dvellon/cueloop/submissions/autodesk_application/APPLICATION_CHECKLIST.md

# Autodesk application submission checklist

Deadline: **September 7, 2026 at 11:59 PM PDT**. Target an internal submission no later than September 6.

## Digital package gate

- [x] Recheck official overview, rules, and organizer guide; record any change.
- [x] Replace only truthful personal facts in application response 5.
- [x] Create the public Hackster opening and paste its URL into response 3.
- [x] Add name, elevator pitch, concept render, BOM, and complete opening story.
- [x] Add Arduino UNO Q, Autodesk Fusion, and PCBWay 3D Printing to Things.
- [x] Complete `HARDWARE_TESTS.md` C-100 through C-109 using `cad/FUSION_WINDOWS_RUNBOOK.md`; attach the genuine native-history `.f3d` only after component/timeline/parameter/geometry/reopen checks and retain the hashed return bundle.
- [x] Attach or embed the system diagram and concept-render disclosure.
- [x] Ensure every “built/measured/tested” claim has evidence; keep future work in future tense.
- [x] Confirm the project is handheld/carryable, carry-on-safe in concept, useful beyond AU, and relevant to Autodesk customers.
- [x] Explain why UNO Q, Fusion, and PCBWay each materially matter.
- [x] Confirm V2 differentiation from CueLoop V1 is explicit.
- [x] Check licenses/provenance for every image, model, code link, and attachment.

## Account-controlled final action

- [ ] Preview the application and project while logged out or in a private browser window.
- [ ] Save a local PDF/screenshot of the live rules if template placeholders remain.
- [ ] Save a copy of each final pasted answer.
- [ ] Submit before the deadline and capture the confirmation page/time.
- [ ] Record the submitted URL and confirmation in `STATUS.md` without personal data.
