dvellon/cueloop/submissions/autodesk_application/APPLICATION_RESPONSES.md

# CueLoop Bridge — Autodesk hardware application responses

**Recommended product name:** CueLoop Bridge  
**One-sentence pitch:** A private, pocketable acoustic awareness bridge that lets creators notice the door, a timer, a collaborator, or a machine finishing in another space—without cloud microphones or stored audio.  
**Short elevator pitch:** Clip on the CueLoop Bridge receiver and leave its detachable CuePod beside what matters. Arduino UNO Q classifies acoustic events locally, checks uncertain evidence over time, and turns confirmed events into a calm visual and haptic cue, while raw audio disappears after inference.

The answers below map to the five prompts in Hackster's organizer-authored application guide. Recheck the live form before pasting.

## 1. What are you going to build?

I am going to build **CueLoop Bridge**, a compact smart accessory that helps people remain aware of important acoustic events occurring somewhere else. The system has two physically related pieces: a small detachable wireless CuePod placed near a door, timer, printer, CNC machine, test rig, or collaborator, and a portable receiver built around Arduino UNO Q. The receiver clips to a belt or bag, hangs from a lanyard, or rests on its integrated desk stand. When the pod hears a selected event, the UNO Q processes it locally and presents a discreet, understandable visual and haptic cue.

The core interaction is deliberately simple: place the pod, choose what matters, and carry the receiver. A wide diffused light communicates urgency and event family, a haptic pattern works while the receiver is clipped or a user is wearing hearing protection, and tactile controls acknowledge, mute, or change priority without opening an app. The CuePod docks mechanically into the receiver for transport; charging contacts and the final power-path design remain measured hardware-development gates. The enclosure is designed as a serviceable Autodesk Fusion assembly with a protected microphone path, USB access, battery restraint, internal board supports, and a clip that doubles as a stand.

CueLoop Bridge is carry-on-safe and useful well beyond Autodesk University. It is intended for designers, makers, technicians, caregivers, people who are deaf or hard of hearing, headphone users, and anyone who moves between acoustically separated spaces.

## 2. What problem will it solve? How is it different, and why is it useful?

Many useful sounds demand attention without requiring anyone to listen continuously: a printer finishes, a timer beeps, someone knocks, water keeps running, or a collaborator calls from another room. Today the person often has to remain nearby, repeatedly check, turn up a loud alert, or place an internet-connected smart speaker or camera in the space. Those compromises are especially costly for people who are deaf or hard of hearing, workers wearing hearing protection, and creators who need to focus deeply.

CueLoop Bridge moves awareness instead of recording a room. Its microphone pod is designed to send short-lived acoustic evidence over the local network to Arduino UNO Q. Edge AI maps the sound into a small user-selected vocabulary, and an uncertainty-aware event engine combines several windows before deciding. A borderline result enters a visible confirmation period rather than creating an instant false alarm. Only a confirmed event, time, confidence, pod location, and user feedback are kept; raw audio is discarded after inference by default.

That combination is the differentiation: detached placement, portable output, local processing, no default recording archive, and deliberate treatment of uncertainty. Smart speakers emphasize general voice services and the cloud. Baby monitors and cameras expose more private context than this task needs. Simple sound classifiers often flash a label for every model spike. CueLoop Bridge is a focused awareness tool that asks, “Is this important enough and certain enough to interrupt this person?”

The product is not a certified alarm, security system, or medical device and will not be marketed as a replacement for required safety equipment. It is useful because it gives users calmer control over ordinary awareness while protecting concentration and privacy.

## 3. Link to the project you have started

https://www.hackster.io/danvellon/cueloop-bridge-69f47f

## 4. How does your solution work? What are the main features? How will UNO Q, Fusion, and PCBWay be used?

The detachable CuePod firmware is designed to use the digital microphone on a Seeed Studio XIAO ESP32S3 Sense to capture 16 kHz mono audio and send sequence-numbered, timestamped frames over a trusted local Wi-Fi network. The Arduino UNO Q Linux side receives those frames into a bounded jitter buffer, normalizes model windows, and runs a lightweight audio-event model locally. A second decision layer then applies per-event confidence thresholds, user priority, temporal confirmation, hysteresis, and cooldown. This prevents a single uncertain window from becoming an immediate interruption.

When the event engine confirms something important, the Linux application creates a structured event record and updates a local, high-contrast dashboard. Through Arduino Bridge RPC it also sends a compact command to the UNO Q's STM32U585 microcontroller. The MCU owns deterministic LED, haptic, and optional buzzer timing and reads the acknowledgement control even if the higher-level UI is busy. This is a genuine use of the UNO Q's dual-processor architecture: the Qualcomm Linux side handles Wi-Fi, AI, policy, history, and the local interface, while the STM32 handles immediate physical interaction and health indication.

The product's main features are a dockable room-to-room microphone pod; local-first AI; confidence-aware confirmation; user-selected event priority; nonverbal visual and haptic cues; local feedback for later threshold personalization; health/loss/latency diagnostics; and no raw-audio retention by default. A simulator and replay harness make the complete pipeline testable even before hardware is available.

Autodesk Fusion is not an afterthought. It is the source of truth for the mechanical system: named dimensional parameters; CuePod base and lid; protected microphone labyrinth; USB opening; battery cavity and strain relief; XIAO supports; receiver base and lid; UNO Q mounting and connector clearance; diffused alert window; tactile controls; clip/stand hinge; pod dock; fasteners; and assembly clearances. The reviewed generator has produced a genuine native-history preliminary `.f3d`. I inspected its Browser hierarchy, timeline, parameters, sections, clearances, and interference results; verified that one parameter updates all seven microphone ports; and then closed and reopened it cleanly. Physical measurements and fit tests will drive named parameters rather than manual remodels. The final design will add Fusion Electronics for an interconnect/carrier, an assembly and drawing package, and DFM variants.

PCBWay will be used to manufacture the evolved enclosure and, if the carrier proves justified, its PCB/assembly. The first enclosure is designed for a serviceable printed prototype with realistic walls, clearances, M2 fasteners, accessible USB ports, and separate lids. DFM work will compare SLS/MJF-style printing with a future injection-molded split, reduce support and fastener count, add draft and consistent wall sections, define material/finish, and create a repeatable end-of-line fit and function test appropriate to a product that could be built in approximately 750 units.

## 5. Tell us about yourself and why you can complete it

I am an investment banker who spends most of my time on professional work and technology research. My work requires disciplined systems thinking, careful review, and the ability to execute complex projects against deadlines. Outside my professional role, I am a hobbyist hardware and software developer with experience in system design and a willingness to learn across electronics, software, and mechanical design.

CueLoop grew from a recurring personal frustration. When work calls me into another room, I can miss the toaster, microwave, or washing machine finishing and leave something waiting or unattended. A similar problem occurs professionally when a long print job runs out of paper unnoticed: work that appeared to be progressing has actually stopped, creating an avoidable delay. These experiences give me a direct understanding of the problem CueLoop Bridge addresses and a practical focus on making its alerts calm, useful, and reliable.

I have already ordered the core Arduino UNO Q and XIAO Sense hardware, created a simulator-first architecture so shipping cannot stop software work, built a safety and privacy plan, and generated and digitally validated a native parametric Fusion design. My development approach is evidence-driven: simulated, development-computer, UNO Q, and physical-CuePod results are labeled separately, and features that do not meet their evaluation targets will be revised or removed rather than overclaimed. I will use the development period for physical integration, Fusion Electronics, PCBWay enclosure iterations, portable-interaction testing, and a complete reproducible build story.
