dvellon/cueloop/submissions/autodesk_application/PACKAGE_README.md

# CueLoop Bridge preliminary Autodesk application kit

This directory is the source for the September 7, 2026 Autodesk hardware
application. The generated archive records its exact Git commit and per-file
SHA-256 hashes.

## Recommended public project uploads

1. Use `media/20-hero-pod-detached.png` as the cover.
2. Paste `01-HACKSTER_PROJECT_OPENING.md` into the project story and adapt only
   formatting required by Hackster.
3. Enter the items from `02-STARTING_BOM.md` in the Things/BOM interface,
   including Arduino UNO Q, Autodesk Fusion, and PCBWay 3D Printing.
4. Attach `cad/CueLoop_Bridge_Native.f3d`.
5. Add `media/cueloop-bridge-system-diagram.svg` to the story.
6. Add the supporting Fusion renders where they clarify the pod, dock/latch,
   receiver, and clip.
7. Paste the five completed form answers from `00-APPLICATION_RESPONSES.md`.

Required caption for every native Fusion render:

`Fusion native concept render—physical enclosure and fit validation pending.`

The earlier AI-generated image is optional and is retained in `audit-only/`
with its provenance record. It must not be presented as physical evidence.

## Required user-controlled steps

- Preview the project and application while logged out or in a private window.
- Save a screenshot or PDF of the live rules while template placeholders remain.
- Save the final pasted answers and submission confirmation.
- Submit before September 7, 2026 at 11:59 PM PDT.

## Claim boundary

The native Fusion design, software tests, firmware builds, simulations, source
manifests, and returned evidence archives are digitally verified. Physical fit,
latch force, acoustic performance, target inference, RF behavior, power/runtime,
thermal behavior, PCBWay review, and manufacturability remain pending until
observed and recorded.
