dvellon/cueloop/submissions/app_lab/SUBMISSION_METADATA.md

# App Lab submission metadata

## Recommended title

**CueLoop: Private Room-to-Room Sound Awareness with UNO Q Edge AI**

## Short title

**CueLoop**

## Subtitle / short description

**A wireless microphone pod turns selected nearby sounds into uncertainty-aware visual cues—locally, without cloud audio or default recordings.**

## Category strategy

Primary: **Best Social Impact**. CueLoop begins with access for people who are deaf or hard of hearing, then broadens to headphone users, people wearing hearing protection, caregivers, neurodivergent users, and makers monitoring another space. Best in Show is upside, not a different claim.

## One-sentence pitch

CueLoop uses a detachable XIAO microphone pod and both processors of Arduino UNO Q to recognize a small set of important sounds locally, wait for temporal confirmation, and translate them into discreet, understandable cues.

## Tags

`Arduino UNO Q`, `Arduino App Lab`, `edge AI`, `audio classification`, `accessibility`, `assistive technology`, `ESP32S3`, `local-first`, `privacy`, `Python`, `Bridge RPC`, `social impact`

## Cover-image plan

Use an original physical 16:9 hero photograph, not the separate Autodesk V2 concept render. Frame a doorway as the visual divide: the finished CuePod sits in the monitored room in the left third; the UNO Q receiver and dashboard sit in the user's room in the right two-thirds; LED3 shows a recognizable cue color. Keep the dashboard's event name, confidence, and “Local · no recordings” badge legible at 1920 × 1080. Use shallow depth only behind—not across—the hardware and screen. Avoid third-party brand clutter, people who have not consented, copyrighted posters/media, fake compositing, and tiny text.

Capture three cover candidates:

1. physical hero with both spaces connected by the doorway;
2. close receiver/dashboard/LED view with blurred CuePod visible through the doorway;
3. clean overhead parts-to-product layout as a fallback.

The Hackster thumbnail must still read as “remote pod → private local cue” when cropped square. Keep any overlaid title to “CueLoop” plus at most five supporting words. Retain the original camera file and an edit log so ownership is clear.

## Required physical insertion slots

- Final original cover photograph.
- One clear finished-system photo.
- One pigtail/polarity close-up after safe assembly.
- One UNO Q LED/dashboard cue photo.
- One App Lab screenshot during a successful run.
- One schematic image (the repository SVG already exists).
- One quantitative physical result table copied from `HARDWARE_RESULTS.md`.
- Final three-minute video URL.

These are evidence gates, not permission to substitute renders or simulator screenshots for a working physical build.
