dvellon/cueloop/assets/concepts/README.md

# Concept asset provenance

## `cueloop-bridge-cover-concept-v1.png`

- Purpose: Autodesk hardware-application cover concept.
- Created: September 1, 2026 with OpenAI's built-in image-generation tool.
- SHA-256: `5250faefe402c1859e55438c418b68840446958f891675b239d048e5841029f0`
- Evidence label: **AI-generated concept render; not a photograph or proof of completed hardware.**
- Third-party input images: none.
- Required public caption: `CueLoop Bridge concept render—physical enclosure and hardware validation pending.`

Prompt summary: premium 16:9 industrial-design render of a deep-navy portable receiver with coral alert diffuser, tactile controls, integrated clip/stand and pod dock; a smaller microphone pod clipped near a fabrication machine; restrained local signal arcs; no people, logos, text, cloud, camera, exposed electronics, or safety/medical cues.

The exact generation prompt is recorded in the project work log and can be regenerated as a new version. Do not silently replace this file; add `-v2`, `-v3`, and so on.
